runty/TheEndgame2024/001 PCB/GERBER/CHOC V1 V2/bottom-preview.png

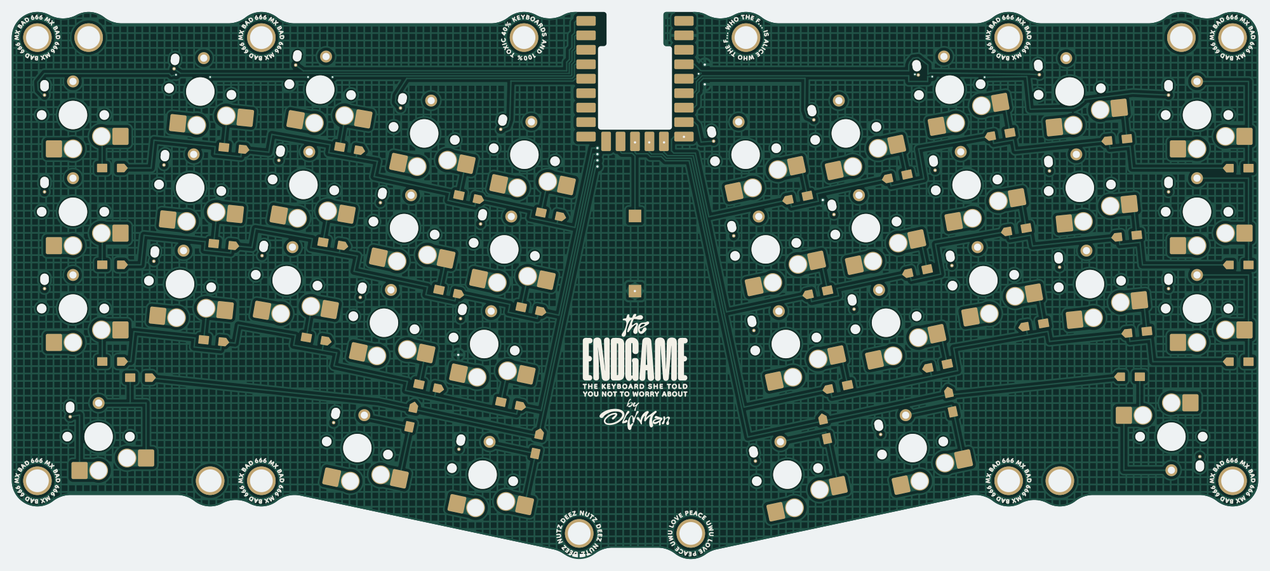
001 PCB/GERBER/CHOC V1 V2/bottom-preview.png
