runty/TheEndgame2024/docs/validation/nice-nano-case/cs-clearance.png

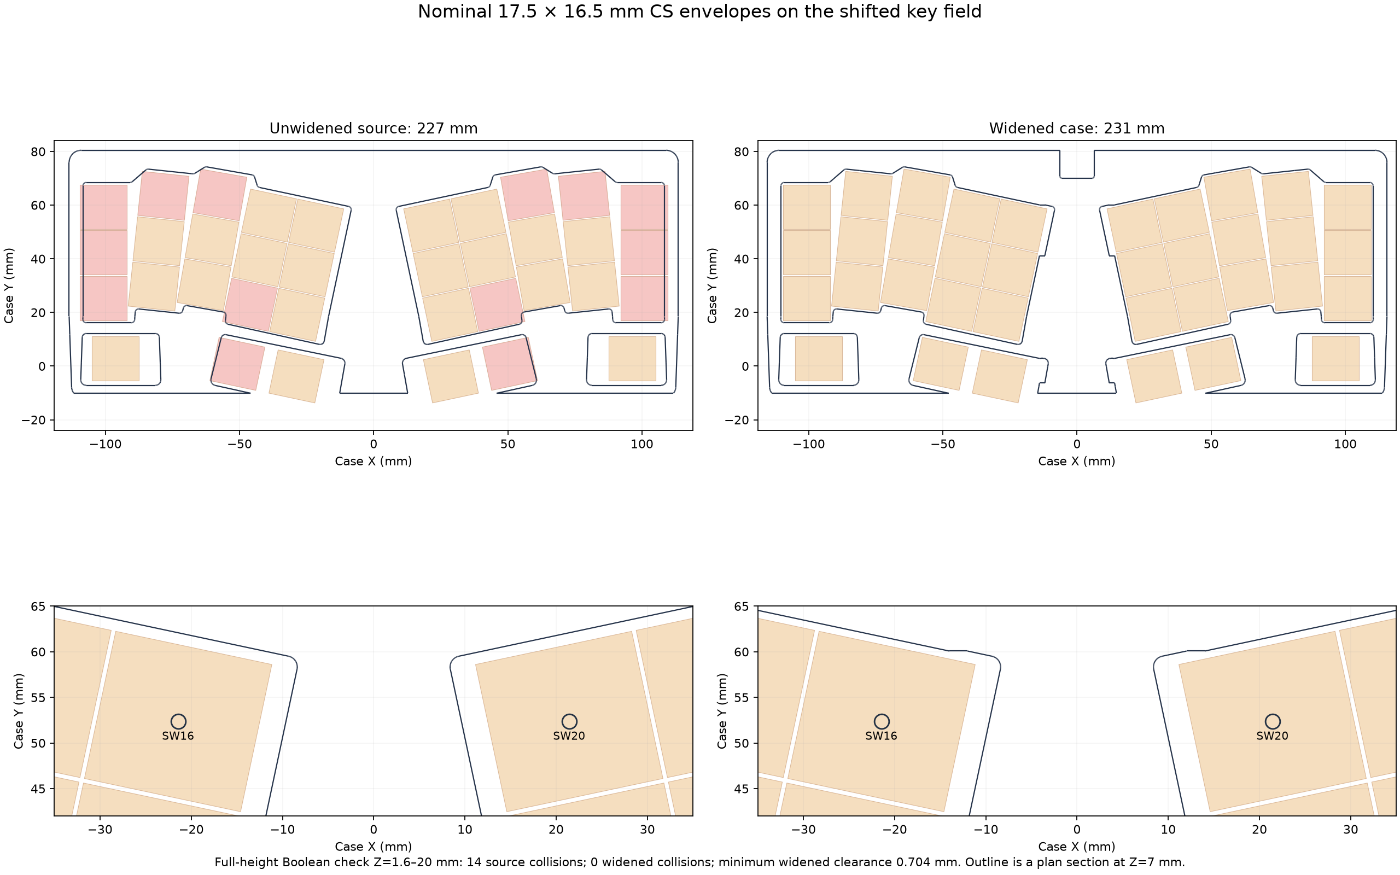
docs/validation/nice-nano-case/cs-clearance.png
