runty/TheEndgame2024/docs/validation/nice-nano-pcb/outer-key-symmetry.png

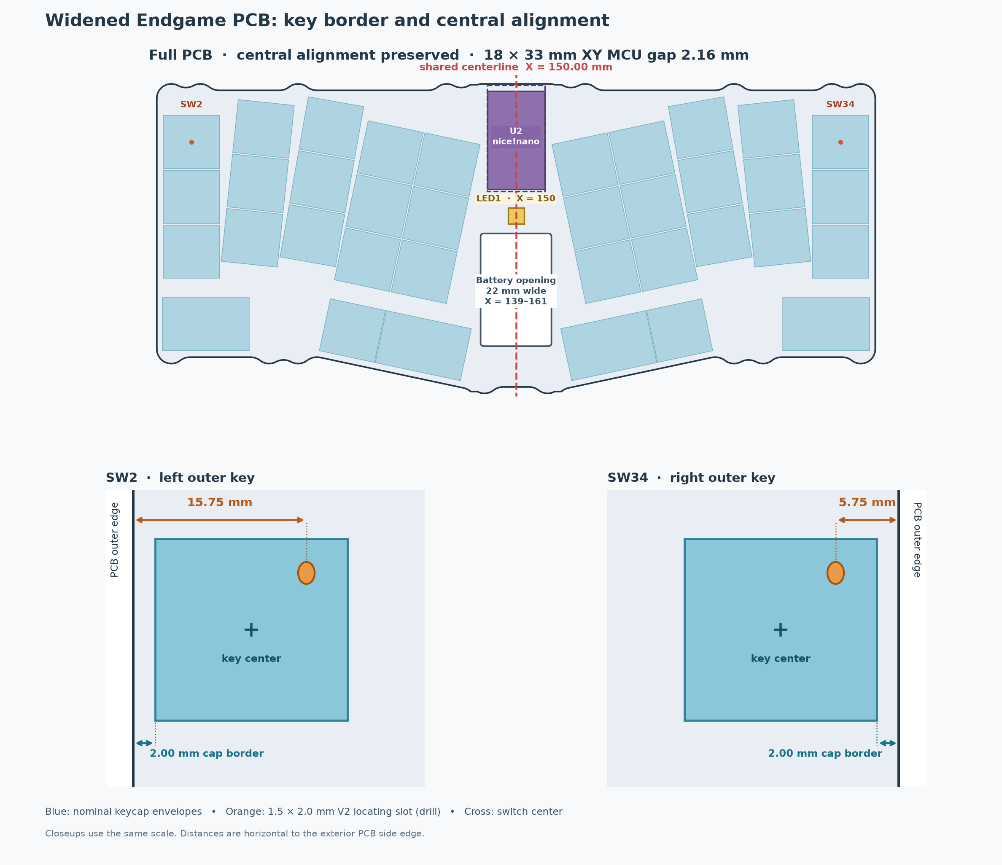
docs/validation/nice-nano-pcb/outer-key-symmetry.png
